lenaschimmel/bestelampe/hardware/driver/Driver Module A/README.md

<!--
SPDX-FileCopyrightText: 2024 Lena Schimmel <mail@lenaschimmel.de>
SPDX-License-Identifier: CC-BY-SA-4.0

[besteLampe!](https://lenaschimmel.de/besteLampe!) © 2024 by [Lena Schimmel](mailto:mail@lenaschimmel.de) is licensed under [CC BY-SA 4.0](http://creativecommons.org/licenses/by-sa/4.0/?ref=chooser-v1)
-->

_See the [README one level above](../README.md) for general info about Driver Modules_

## Driver Module A
This is a module for the Allegro Microsystems A6211 Constant-Current 3-Ampere PWM Dimmable Buck Regulator LED Driver.

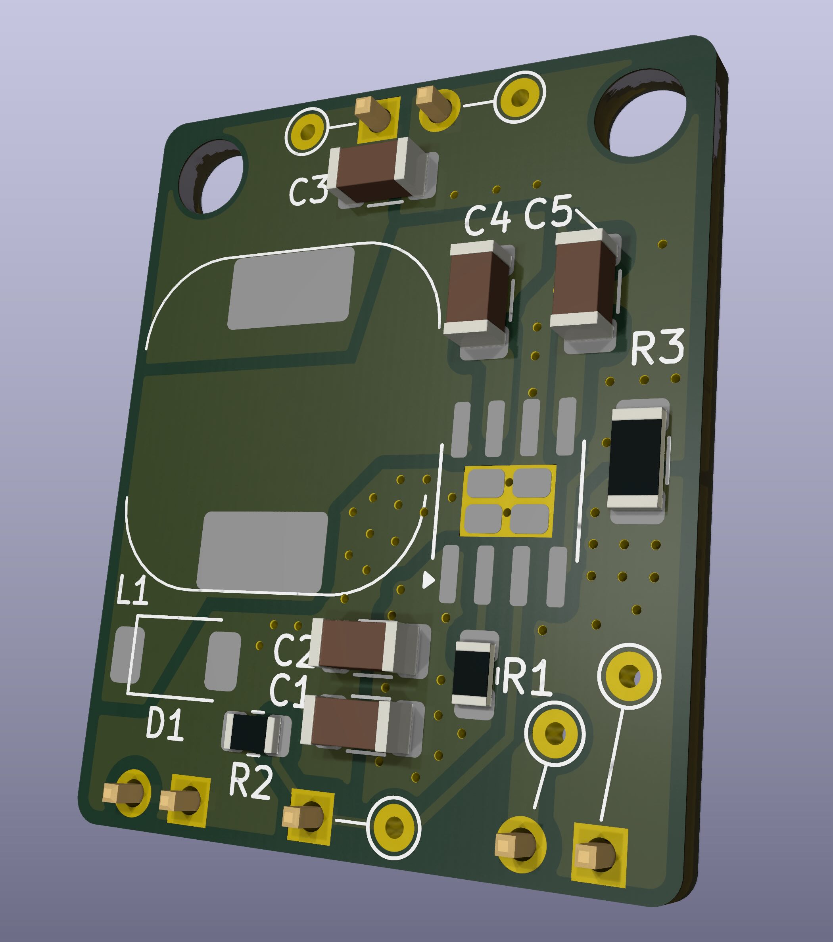
[picture p18: assets/driver_board_a.jpg]
Rendering of the driver Board from KiCad. The rendered board is green, even though the ones I ordered will be purple. Small SMD components are shown, but the three biggest and most important parts are missing.
