lenaschimmel/bestelampe/hardware/driver/Driver Module X (template)/README.md

<!--
SPDX-FileCopyrightText: 2024 Lena Schimmel <mail@lenaschimmel.de>
SPDX-License-Identifier: CC-BY-SA-4.0

[besteLampe!](https://lenaschimmel.de/besteLampe!) © 2024 by [Lena Schimmel](mailto:mail@lenaschimmel.de) is licensed under [CC BY-SA 4.0](http://creativecommons.org/licenses/by-sa/4.0/?ref=chooser-v1)
-->

_See the [README one level above](../README.md) for general info about Driver Modules_

## Driver Module X (Template)
This should be the template for future driver boards, and Driver Board A is actually based on this one.

But I think this template might be scrapped soon, and I should make a new one based on Driver Board A.

Also, the space was already very tight for Driver Board A, so that other driver boards might need a bigger PCB anyway.
