lenaschimmel/bestelampe/hardware/ledmodule/LED_Driver/README.md

<!--
SPDX-FileCopyrightText: 2024 Lena Schimmel <mail@lenaschimmel.de>
SPDX-License-Identifier: CC-BY-SA-4.0

[besteLampe!](https://lenaschimmel.de/besteLampe!) © 2024 by [Lena Schimmel](mailto:mail@lenaschimmel.de) is licensed under [CC BY-SA 4.0](http://creativecommons.org/licenses/by-sa/4.0/?ref=chooser-v1)
-->
## LED Driver
Early work on a small, inexpensive module based on the TI TPS92200. The LED Module C will need 6 to 12 of those to work.

It's not yet decided if this modul will be kept in this KiCad project, or merged into either LED Module C some other module.
