lenaschimmel/bestelampe/hardware/abl/Feather C6/factory-reset/README.md

## Factory Reset file - ESP32-C6 Feather - STEMMA QT

This is the factory reset file for the ESP32-C6 Feather - STEMMA QT.
