lenaschimmel/bestelampe/assets/cie-diagram-1.jpg

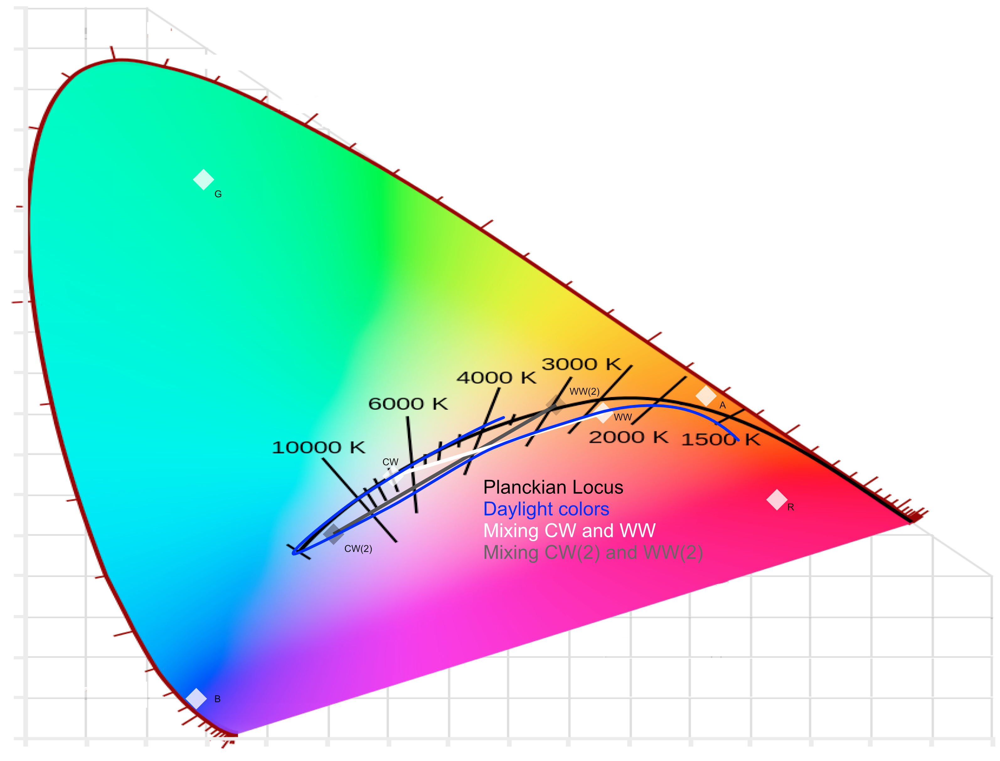
assets/cie-diagram-1.jpg
