lenaschimmel/bestelampe/software/slint-ui/assets/img/CIE1931xy-1927px.png

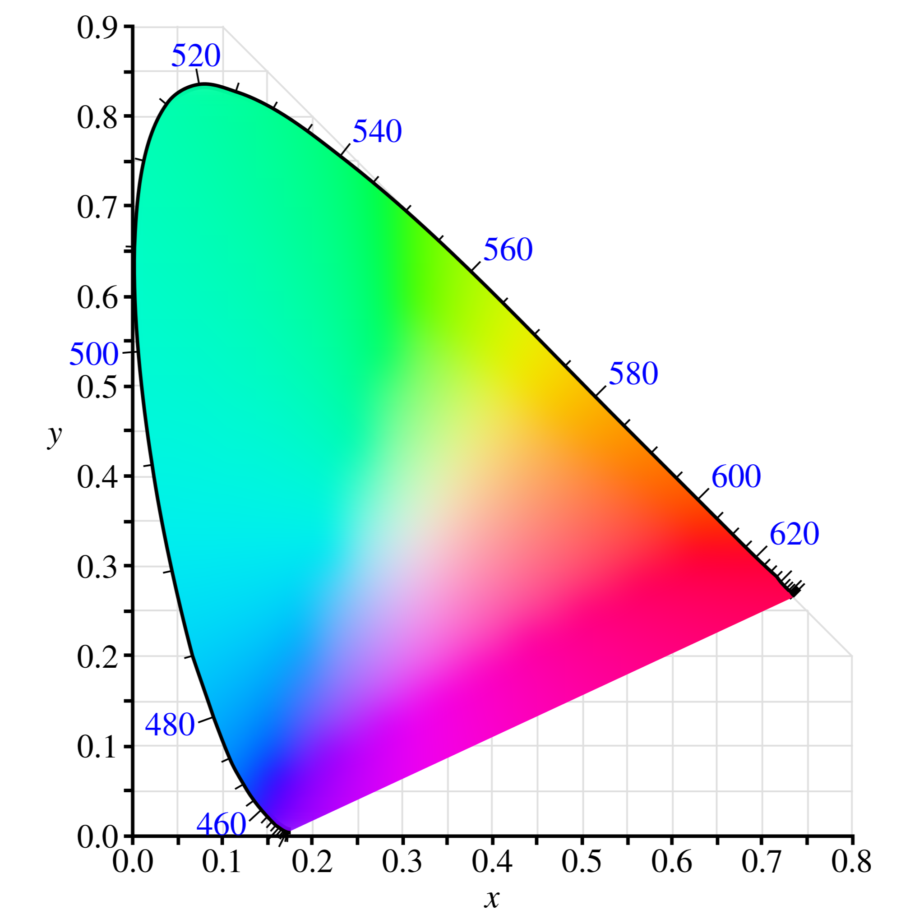
software/slint-ui/assets/img/CIE1931xy-1927px.png
