lenaschimmel/bestelampe/hardware/round/ringuntenkleb.stl

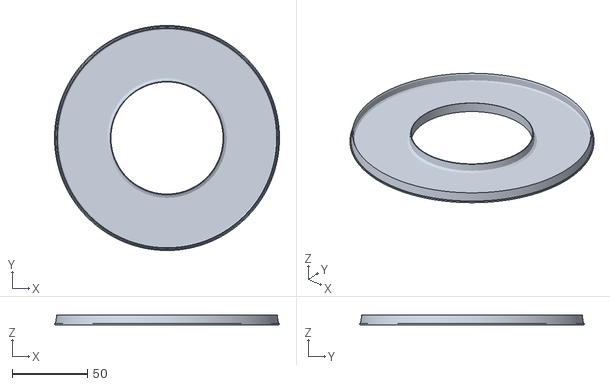
[picture p39: CAD file, 2024-01-30]
hardware/round/ringuntenkleb.stl
149.8 x 149.8 x 6.32
