lenaschimmel/bestelampe/hardware/round/Hauptreflektor.stl

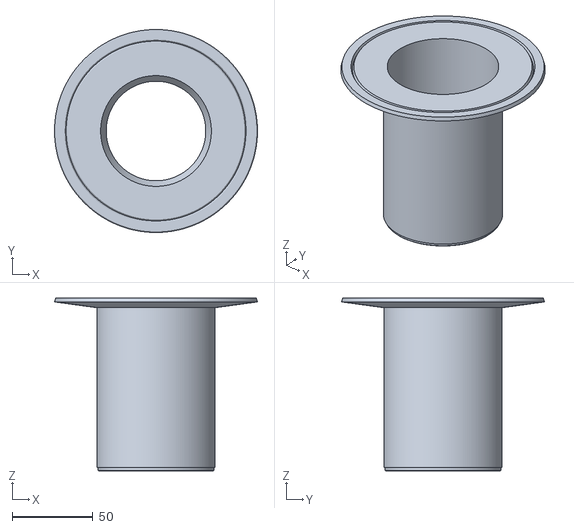
[picture p40: CAD file, 2024-01-30]
hardware/round/Hauptreflektor.stl
126.0 x 126.0 x 107.2
