lenaschimmel/bestelampe/hardware/round/Inlay.stl

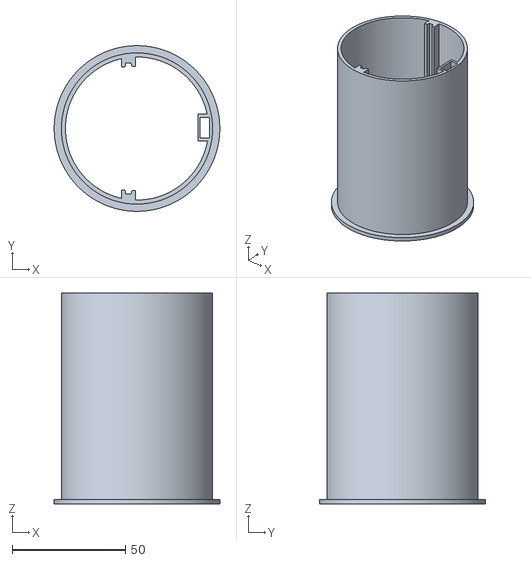
[picture p41: CAD file, 2024-01-30]
hardware/round/Inlay.stl
73.0 x 73.0 x 93.0
