lenaschimmel/bestelampe/hardware/round/HausnummernscheibeMassiv.stl

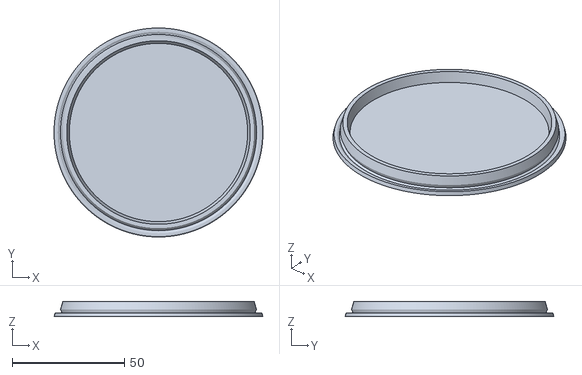
[picture p42: CAD file, 2024-01-30]
hardware/round/HausnummernscheibeMassiv.stl
92.9 x 92.9 x 6.80
