lenaschimmel/bestelampe/hardware/round/rings.stl

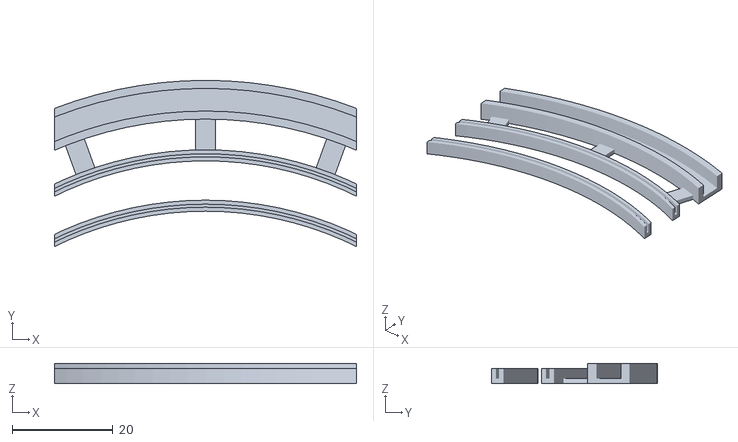
[picture p43: CAD file, 2024-01-30]
hardware/round/rings.stl
60.0 x 33.0 x 4.00
