lenaschimmel/bestelampe/hardware/ledmodule/LED_Test_Module/README.md

<!--
SPDX-FileCopyrightText: 2024 Lena Schimmel <mail@lenaschimmel.de>
SPDX-License-Identifier: CC-BY-SA-4.0

[besteLampe!](https://lenaschimmel.de/besteLampe!) © 2024 by [Lena Schimmel](mailto:mail@lenaschimmel.de) is licensed under [CC BY-SA 4.0](http://creativecommons.org/licenses/by-sa/4.0/?ref=chooser-v1)
-->

This is a simple "breakout board" for a single SMD LED and offers various sizes and 
footprints. Nothing fancy.

You can also add up to three SMD resistors.

## TODO
I should have added through-holes to solder regular resistors as well.
