lenaschimmel/bestelampe/software/bestelampe/src/task/presence.rs

// SPDX-FileCopyrightText: 2024 Lena Schimmel <mail@lenaschimmel.de>
// SPDX-License-Identifier: CERN-OHL-S-2.0+
// This file is part of besteLampe!.
// 
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
// besteLampe! is distributed in the hope that it will be useful, but WITHOUT ANY WARRANTY; 
// without even the implied warranty of MERCHANTABILITY or FITNESS FOR A PARTICULAR PURPOSE. 
// See the GNU General Public License for more details.
// 
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
use crate::prelude::*;

use std::time::Duration;
use std::sync::{Arc, RwLock};

use enumset::EnumSet;
use esp_idf_hal::rmt::{RmtChannel, CHANNEL2};
use esp_idf_hal::{
    prelude::*,
    delay::TickType,
    gpio::AnyIOPin,
    uart, 
    uart::{UART1, config::*},
};

use mr24hpc1::{mr_parser, Frame, HumanPresence, Motion};

use esp_idf_hal::{
    delay::FreeRtos,
    rmt::{
        FixedLengthSignal, PinState, Pulse, PulseTicks, Receive, RmtReceiveConfig,
        RmtTransmitConfig, RxRmtDriver, TxRmtDriver,
    },
};



#[named]
pub fn test_presence_sensor_rmt(
    pin_rx: AnyIOPin,
    pin_tx: AnyIOPin,
    rmt_channel: CHANNEL2, 
    light_brightness_target: Arc<RwLock<f32>>,
) ->  Result<()>  {
        // Oszi-Messung vom Präsenzsensor:
        // Bitlänge 8,7µs
        // Burst-Länge 860µs
        // Also ca. 100 Roh-Bits = 10 Byte.

        let config = RmtReceiveConfig::new()
            .idle_threshold(700u16) // A full byte of 0s is just 311 ticks
            .clock_divider(20) // should be 250ns
            .filter_ticks_thresh(8) // equals 2µs < 1/4 of a bit
        ;
         
        let mut rx = RxRmtDriver::new(
            rmt_channel,
            pin_rx,
            &config,
            250,
        )?;

        rx.start()?;

        let mut pulses = [(Pulse::zero(), Pulse::zero()); 250];
        let _ = std::thread::Builder::new()
            .stack_size(10000)
            .spawn(move || loop {

                // See sdkconfig.defaults to determine the tick time value ( default is one tick = 10 milliseconds)
                // Set ticks_to_wait to 0 for non-blocking
                let receive = rx.receive(&mut pulses, 10000).unwrap();

                if let Receive::Read(length) = receive {
                    let pulses = &pulses[..length];

                    for (pulse0, pulse1) in pulses {
                        println!("0={pulse0:?}, 1={pulse1:?}");
                    }
                }

                // Example output from Presence Sensor:
                // 0=Pulse { ticks: PulseTicks(34), pin_state: Low }, 1=Pulse { ticks: PulseTicks(70), pin_state: High }
                // 0=Pulse { ticks: PulseTicks(69), pin_state: Low }, 1=Pulse { ticks: PulseTicks(35), pin_state: High }
                // 0=Pulse { ticks: PulseTicks(34), pin_state: Low }, 1=Pulse { ticks: PulseTicks(35), pin_state: High }
                // 0=Pulse { ticks: PulseTicks(35), pin_state: Low }, 1=Pulse { ticks: PulseTicks(34), pin_state: High }
                // 0=Pulse { ticks: PulseTicks(35), pin_state: Low }, 1=Pulse { ticks: PulseTicks(34), pin_state: High }
                // 0=Pulse { ticks: PulseTicks(70), pin_state: Low }, 1=Pulse { ticks: PulseTicks(69), pin_state: High }
                // 0=Pulse { ticks: PulseTicks(35), pin_state: Low }, 1=Pulse { ticks: PulseTicks(34), pin_state: High }
                // 0=Pulse { ticks: PulseTicks(35), pin_state: Low }, 1=Pulse { ticks: PulseTicks(35), pin_state: High }
                // 0=Pulse { ticks: PulseTicks(277), pin_state: Low }, 1=Pulse { ticks: PulseTicks(69), pin_state: High }
                // 0=Pulse { ticks: PulseTicks(35), pin_state: Low }, 1=Pulse { ticks: PulseTicks(69), pin_state: High }
                // 0=Pulse { ticks: PulseTicks(208), pin_state: Low }, 1=Pulse { ticks: PulseTicks(34), pin_state: High }
                // 0=Pulse { ticks: PulseTicks(312), pin_state: Low }, 1=Pulse { ticks: PulseTicks(35), pin_state: High }
                // 0=Pulse { ticks: PulseTicks(34), pin_state: Low }, 1=Pulse { ticks: PulseTicks(35), pin_state: High }
                // 0=Pulse { ticks: PulseTicks(242), pin_state: Low }, 1=Pulse { ticks: PulseTicks(35), pin_state: High }
                // 0=Pulse { ticks: PulseTicks(35), pin_state: Low }, 1=Pulse { ticks: PulseTicks(34), pin_state: High }
                // 0=Pulse { ticks: PulseTicks(243), pin_state: Low }, 1=Pulse { ticks: PulseTicks(34), pin_state: High }
                // 0=Pulse { ticks: PulseTicks(35), pin_state: Low }, 1=Pulse { ticks: PulseTicks(35), pin_state: High }
                // 0=Pulse { ticks: PulseTicks(104), pin_state: Low }, 1=Pulse { ticks: PulseTicks(69), pin_state: High }
                // 0=Pulse { ticks: PulseTicks(69), pin_state: Low }, 1=Pulse { ticks: PulseTicks(35), pin_state: High }
                // 0=Pulse { ticks: PulseTicks(104), pin_state: Low }, 1=Pulse { ticks: PulseTicks(34), pin_state: High }
                // 0=Pulse { ticks: PulseTicks(35), pin_state: Low }, 1=Pulse { ticks: PulseTicks(35), pin_state: High }
                // 0=Pulse { ticks: PulseTicks(34), pin_state: Low }, 1=Pulse { ticks: PulseTicks(35), pin_state: High }
                // 0=Pulse { ticks: PulseTicks(34), pin_state: Low }, 1=Pulse { ticks: PulseTicks(35), pin_state: High }
                // 0=Pulse { ticks: PulseTicks(35), pin_state: Low }, 1=Pulse { ticks: PulseTicks(69), pin_state: High }
                // 0=Pulse { ticks: PulseTicks(139), pin_state: Low }, 1=Pulse { ticks: PulseTicks(34), pin_state: High }
                // 0=Pulse { ticks: PulseTicks(35), pin_state: Low }, 1=Pulse { ticks: PulseTicks(0), pin_state: High }

                FreeRtos::delay_ms(5);
            });

    Ok(())
}

#[named]
pub fn test_presence_sensor(
    pin_rx: AnyIOPin,
    pin_tx: AnyIOPin,
    uart_device: UART1, 
    light_brightness_target: Arc<RwLock<f32>>,
) ->  Result<()>  {
    info!(target: function_name!(), "Connecting to GPIO 17 to sample the sensor");

    std::thread::sleep(core::time::Duration::from_millis(500));

    // Initialize config manually, because `uart::config::Config::default()`
    // crashes on ESP32-C6 due to an invalid SourceClock.
    let config = uart::config::Config {
        baudrate: Hertz(115_200),
        data_bits: DataBits::DataBits8,
        parity: Parity::ParityNone,
        stop_bits: StopBits::STOP1,
        flow_control: FlowControl::None,
        flow_control_rts_threshold: 122,
        source_clock: SourceClock::Crystal,
        intr_flags: EnumSet::EMPTY,
        event_config: EventConfig::new(),
        rx_fifo_size: 128 * 2,
        tx_fifo_size: 128 * 2,
        queue_size: 0,
        _non_exhaustive: (),
    };

    let uart: uart::UartDriver = uart::UartDriver::new(
        uart_device,
        pin_tx,
        pin_rx,
        Option::<AnyIOPin>::None,
        Option::<AnyIOPin>::None,
        &config
    )?;

    let mut cycles_without_data = 0;
    info!(target: function_name!(), "Try to read stuff...");
    loop {
        let mut buf = [0_u8; 20];
        let len: usize = uart.read(&mut buf, TickType::from(Duration::from_millis(50)).ticks())?;
        
        if len >= 9 {
            cycles_without_data = 0;
            match mr_parser(&buf[0..len]) {
                Ok((_, frame)) => {
                    info!(target: function_name!(), "Parsed presence data: {:?}", frame);
                    match frame {
                        Frame::HumanPresenceReport(HumanPresence::BodyMovementParameter(movement)) => {
                            info!(target: function_name!(), "Movement: {:?}", movement);
                           // *light_brightness_target.write().unwrap() = movement as f32;
                        },
                        Frame::HumanPresenceReport(HumanPresence::MotionInformation(motion)) => {
                            info!(target: function_name!(), "Motion: {:?}", motion);
                            *light_brightness_target.write().unwrap() = match motion {
                                Motion::None => 0.2,
                                Motion::Motionless => 0.8,
                                Motion::Active => 2.0,
                            }
                        },
                        _ => {

                        }
                    }
                },
                Err(_) => {
                    warn!(target: function_name!(), "Error while parsing presence data '{:x?}'", buf);
                },
            }
        } else if len > 0 {
            warn!(target: function_name!(), "Short presence data '{:x?}'", buf);
            cycles_without_data = 0;
        } else {
            cycles_without_data += 1;
            if cycles_without_data > 100 && cycles_without_data % 100 == 0 {
                warn!(target: function_name!(), "Had {} cycles without any data.", cycles_without_data);
            }
        }
    }
}
